nandojve/atusb/atben/case/V0.1 view 1.png

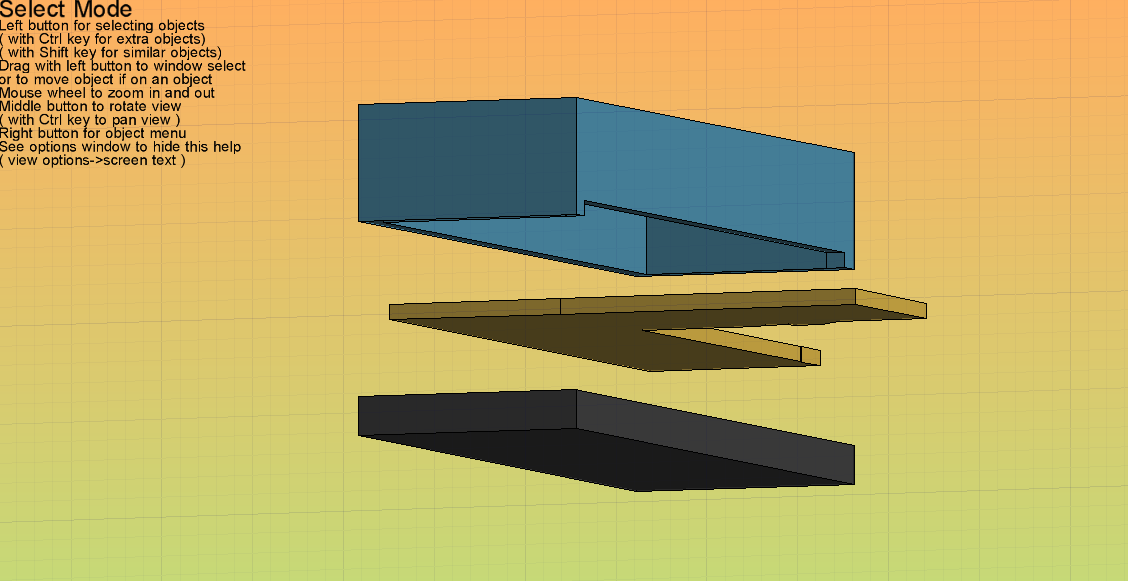
atben/case/V0.1 view 1.png
