nandojve/atusb/atben/case/V01 view 2.png

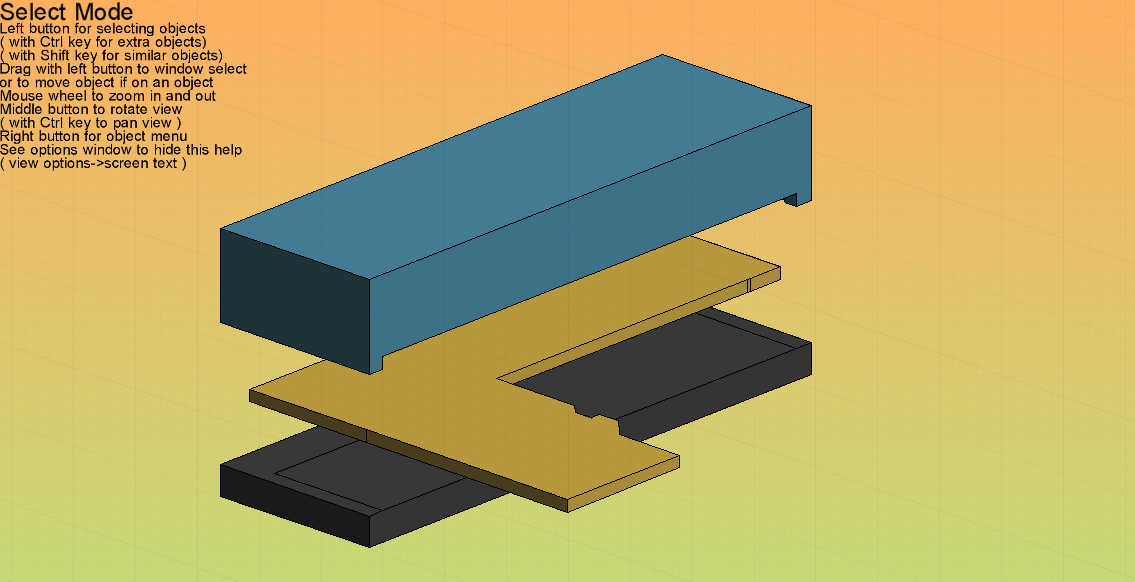
atben/case/V01 view 2.png
