nandojve/atusb/atben/tests/psd-2430.png

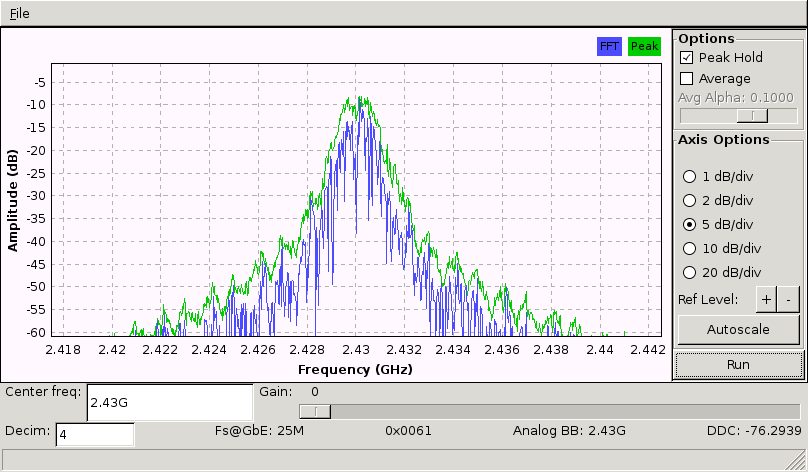
atben/tests/psd-2430.png
