nandojve/atusb/ants/ants.sch

## KiCad design ants/ants.sch (2010-11-06)

Schematic: ants.sch

Parts:
ANT1: 50R; meander
P1: U.FL; u.fl-receptacle
R1: 0; 0402
