nandojve/atusb/atben/atben.sch

## KiCad design atben/atben.sch (2012-05-29, an earlier design)

Schematic: atben.sch

Parts:
ANT1: 50R; meander
B1: 2450FB15L0001; 0805-6
C1, C2: 22pF/RF; 0402
C3, C4, C5, C6: 1uF; 0402
C10, C11: 12pF; 0402
C12: NC; 0402
P1: TST; PAD_2mm
P2: CONN_8; 10-card
R1: 0R; 0402
U1: AT86RF231; QFN32-VHHD6
X1: 16MHz; xtal4-3.2mmx2.5mm
