nandojve/atusb/atusb-pgm/atusb-pgm.sch

## KiCad design atusb-pgm/atusb-pgm.sch (2011-02-28)

Schematic: atusb-pgm.sch

Parts:
D1: LTST-C190KFKT; 0603
P1, P2, P3, P4, P5, P6: CONN_1; PAD_80x80
P7, P8, P9, P10, P11, P12, P13, P14: CONN_1; PAD_2mm
R1: 100; 0603

Notes on the sheet:
For red, use LTST-C190KRKT (631 nm)
LTST-C190KFKT is yellow/orange (605 nm)
