nandojve/atusb/atusb-sil/atrf.sch

## KiCad design atusb-sil/atrf.sch (2011-01-23)

Schematic: atrf.sch

Parts:
ANT1: 50R; meander
B1: 2450FB15L0001; 0805-6
C3, C8, C9: 22pF/RF; 0402
C10, C11, C12, C13: 1uF; 0402
C14, C15: 12pF; 0402
C16: NC; 0402
P16: TST; PAD_60x60
R3: 0R; 0402
U2: AT86RF231; QFN32-VHHD-6
X1: 16MHz; xtal4-3.2mmx2.5mm
