nandojve/atusb/atusb-sil/usb.sch

## KiCad design atusb-sil/usb.sch (2011-01-23)

Schematic: usb.sch

Parts:
C1: 1uF; 0402
C2: 100nF; 0402
CON1: USB_A_PLUG
D1: LTST-C190KRKT; 0603
P11, P12, P13, P14: CONN_1; PAD_60x60
R1: 68; 0402
U1: C8051F326; QFN28-SiLabs
VR1, VR2, VR3: 5V6; 0402

Notes on the sheet:
USB 2.0 limits the capacitative load on full-speed drivers to 50 pF.
ID: open 1008xx, GND: 1012xx
Space P11 through P14 at 100 mil interval close to board edge to allow use with a 0.1" header soldered to the board.
USB
