nandojve/atusb/atusb/usb.sch

## KiCad design atusb/usb.sch (2016-08-01, an earlier design)

Schematic: usb.sch

Parts:
C1: 10uF; 0603
C2: 1uF; 0402
CON1: USB_A_PLUG
D1: LTST-C190KRKT; 0603
P11, P12, P13, P14, P15, P16: CONN_1; PAD_60x60
R1: 180; 0402
R4, R5: 22; 0402
U1: ATMEGA32U2; QFN32-VHHD-2
VR1, VR2, VR3: 5.5Vdc; 0402

Notes on the sheet:
USB 2.0 limits the capacitative load on full-speed drivers to 50 pF.
Space P11 through P16 at 100 mil interval close to board edge to allow use with a 0.1" header soldered to the board.
USB
