nandojve/atusb/cntr/cntr.sch

## KiCad design cntr/cntr.sch (2010-11-06)

Schematic: cntr.sch

Parts:
C1: 100nF; 0603
C2: 1uF; 0603
CON1: USB_A_PLUG; USB_A_PLUG_SMT
D1: LTST-C190KRKT; 0603
P1, P2, P3, P4, P5, P6, P7: CONN_1; PAD_120x60
R1: 1k; 0603
R2: 330; 0603
R3: 68; 0603
U1: C8051F320; LQFP32
VR1, VR2, VR3, VR4: 5V6; 0402
